ciaassured/eveningstar-hardware/assets/bus_drive_resistors/0ohm.png

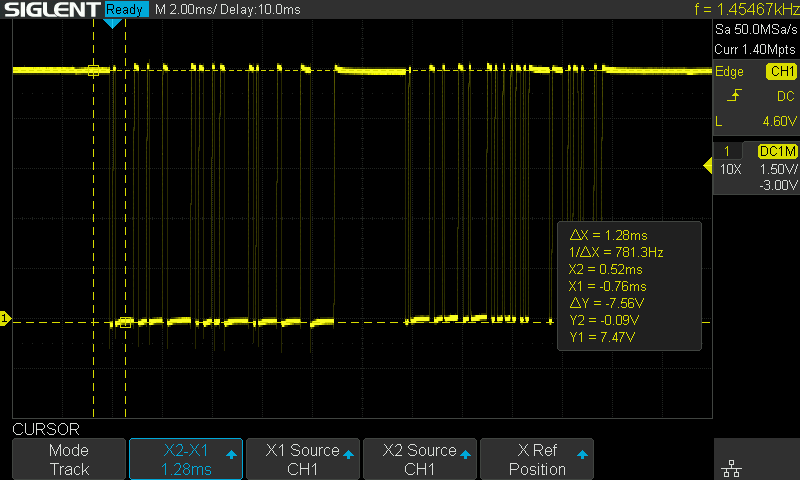
assets/bus_drive_resistors/0ohm.png
