ciaassured/eveningstar-hardware/assets/bus_drive_resistors/1800ohm.png

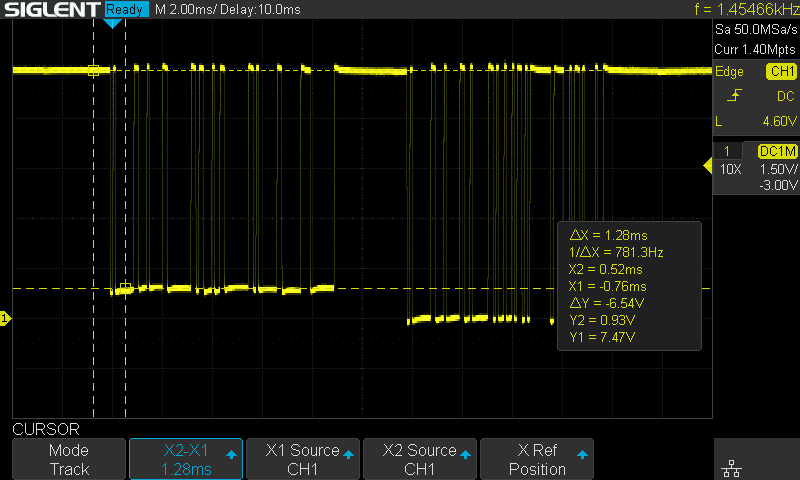
assets/bus_drive_resistors/1800ohm.png
